xoseperez/espurna-board/espurna-h/v0.8/espurna-h-v0.8.20171028-bottom2.png

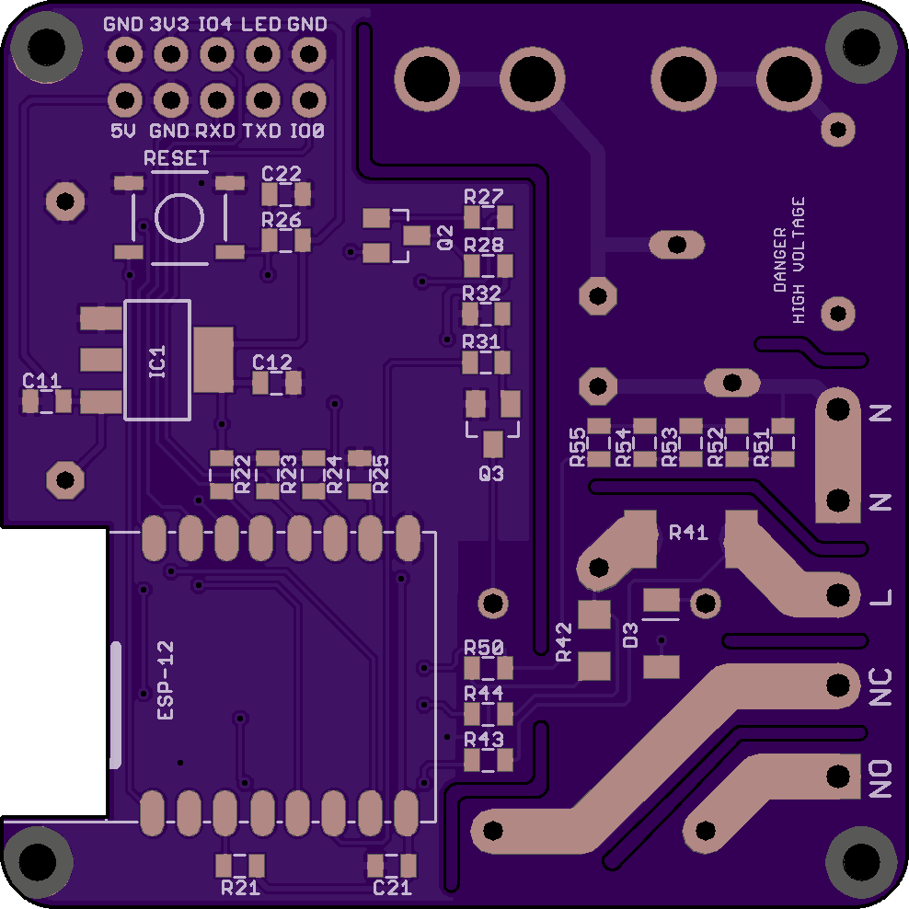
espurna-h/v0.8/espurna-h-v0.8.20171028-bottom2.png
