xoseperez/espurna-board/espurna-h/v0.8/espurna-h-v0.8.20171028-top2.png

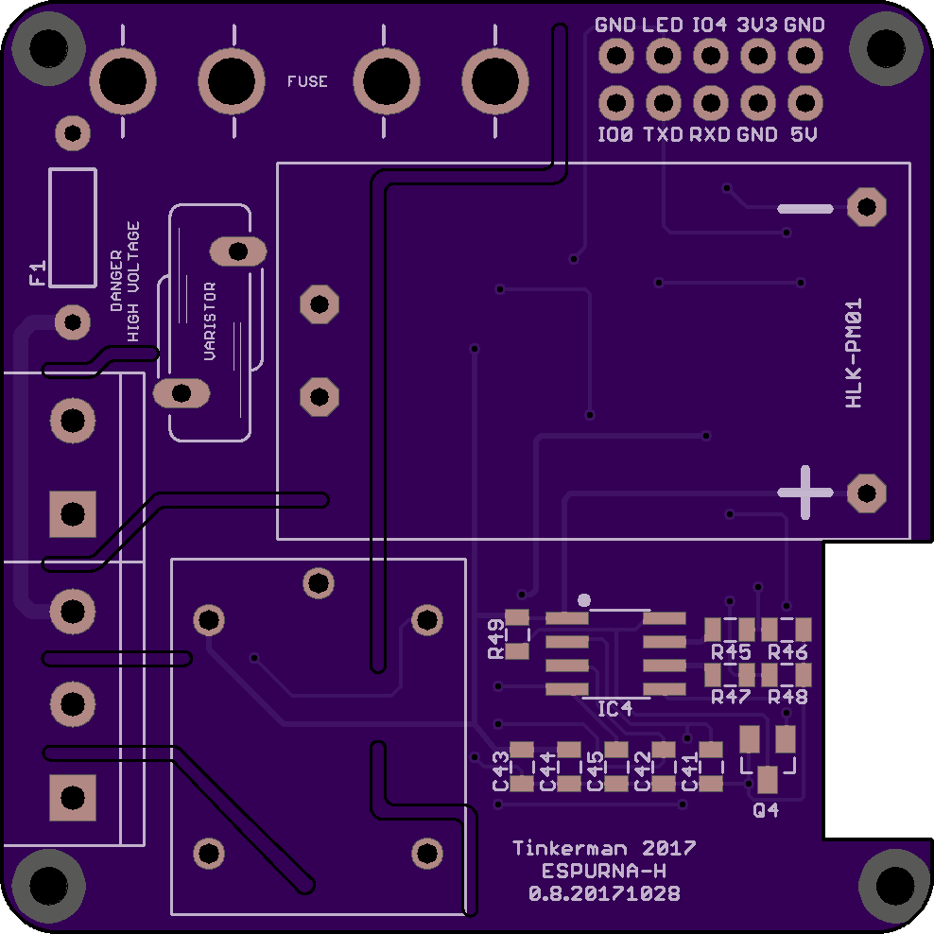
espurna-h/v0.8/espurna-h-v0.8.20171028-top2.png
