xoseperez/espurna-board/images/20170327_233154s.jpg

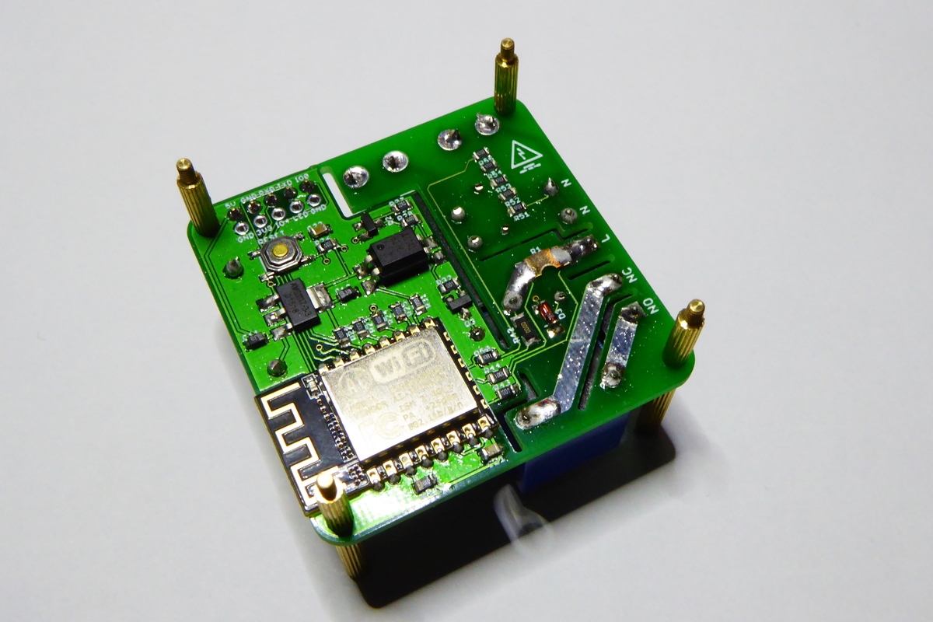
images/20170327_233154s.jpg
