xoseperez/espurna-board/images/20170406_110434s.jpg

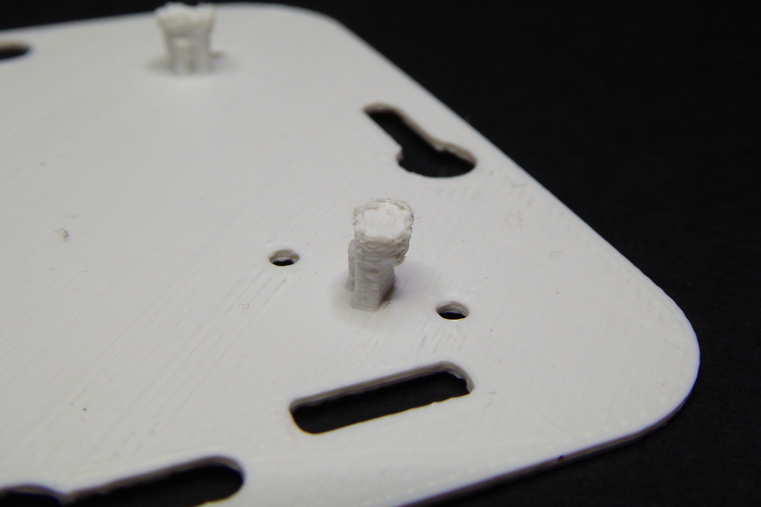
images/20170406_110434s.jpg
