xoseperez/espurna-board/images/espurna_h.base.openscad.png

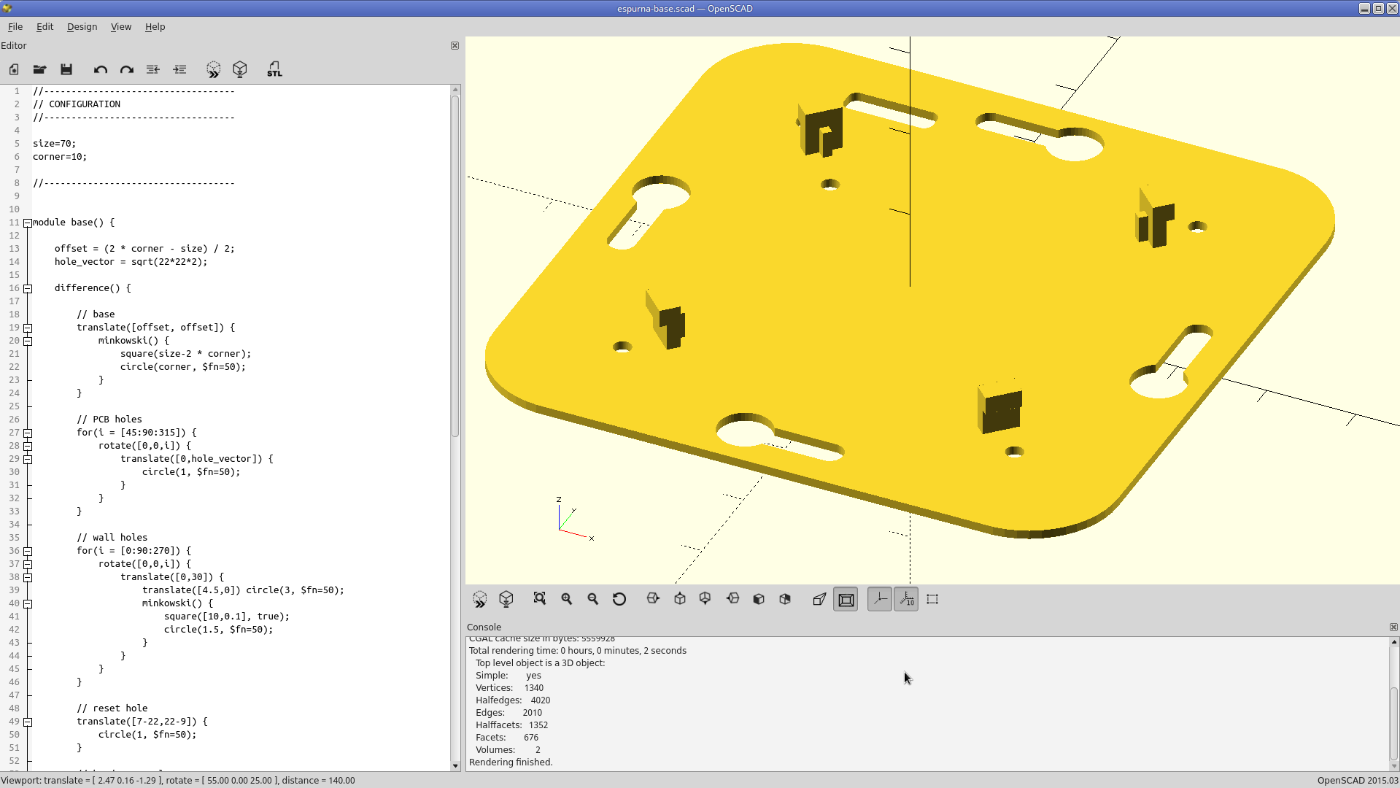
images/espurna_h.base.openscad.png
